kris701/CAI/STL Files/Snapmaker-Backplate-Extension/SnapmakerBackplateExtension_Case.stl

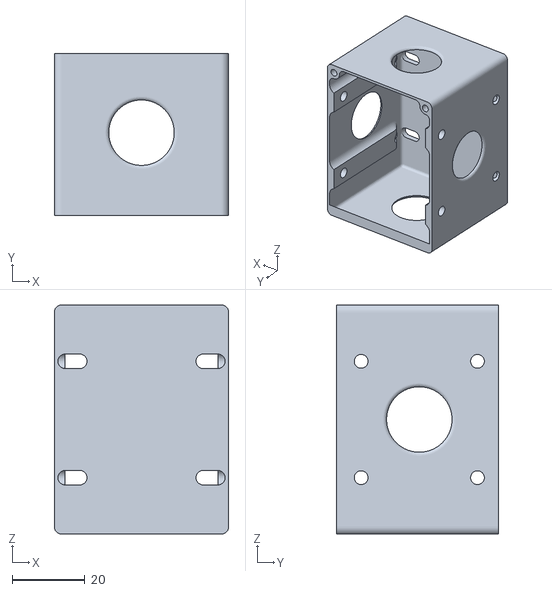
[picture p15: CAD file, 2021-12-27]
STL Files/Snapmaker-Backplate-Extension/SnapmakerBackplateExtension_Case.stl
48.0 x 44.5 x 63.0
