kris701/CAI/STL Files/Snapmaker-Backplate-Extension/SnapmakerBackplateExtension_SideCap.stl

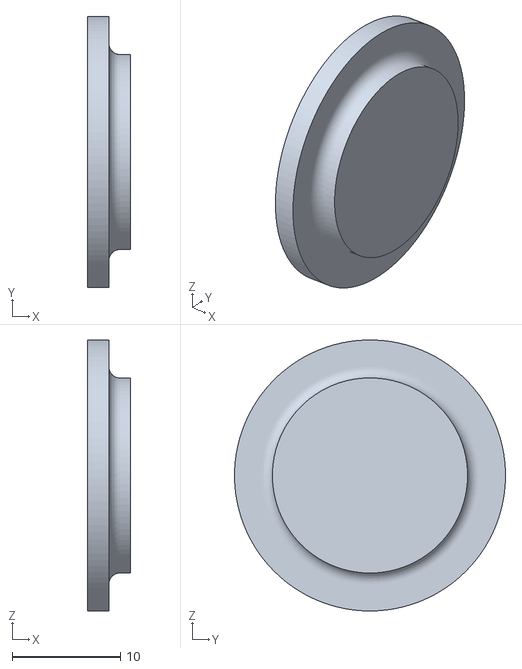
[picture p16: CAD file, 2021-12-27]
STL Files/Snapmaker-Backplate-Extension/SnapmakerBackplateExtension_SideCap.stl
4.00 x 25.0 x 25.0
