kris701/CAI/STL Files/Screw-Module-Mk1/ScrewModuleMk1_MainBody.stl

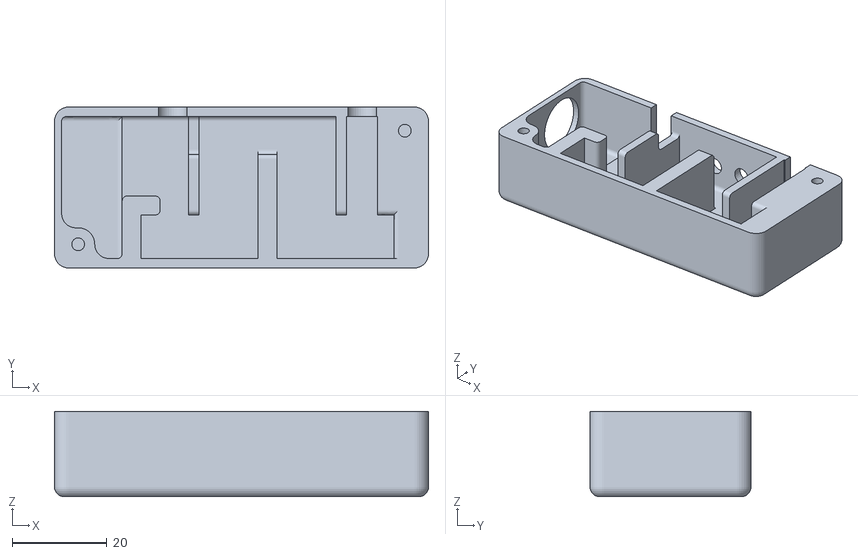
[picture p17: CAD file, 2021-12-27]
STL Files/Screw-Module-Mk1/ScrewModuleMk1_MainBody.stl
79.0 x 34.0 x 18.0
