kris701/CAI/STL Files/Screw-Module-Mk1/ScrewModuleMk1_Lid.stl

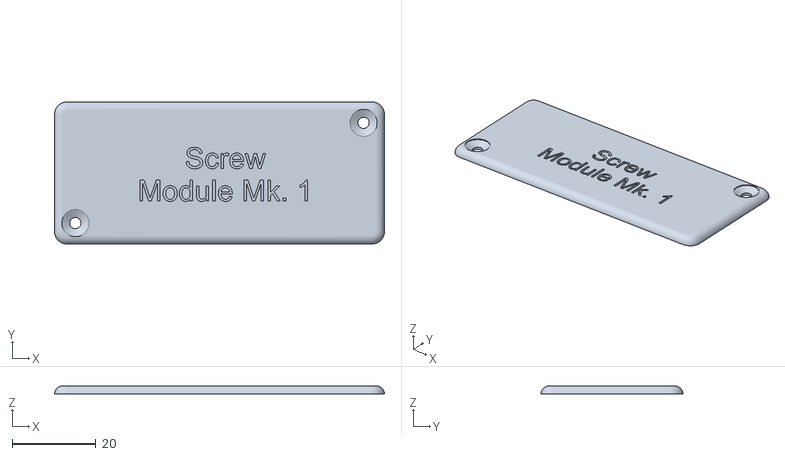
[picture p18: CAD file, 2021-12-27]
STL Files/Screw-Module-Mk1/ScrewModuleMk1_Lid.stl
79.0 x 34.0 x 2.00
